xjh186164-del/Wearable-sEMG-IMU-gesture-recognition/Data/training_runs/p001_ablation_20260908/retrained/fixed_50_50/seed_20260821/test_predictions.csv

dataset_index | session_id | trial_id | true_index | true_label | fixed_50_50_index | fixed_50_50_label
10472 | S003_D08_R01 | 1 | 0 | REST | 0 | REST
10473 | S003_D08_R01 | 1 | 0 | REST | 0 | REST
10474 | S003_D08_R01 | 1 | 0 | REST | 0 | REST
10475 | S003_D08_R01 | 1 | 0 | REST | 0 | REST
10476 | S003_D08_R01 | 1 | 0 | REST | 0 | REST
10477 | S003_D08_R01 | 1 | 0 | REST | 0 | REST
10478 | S003_D08_R01 | 1 | 0 | REST | 0 | REST
10479 | S003_D08_R01 | 1 | 0 | REST | 0 | REST
10480 | S003_D08_R01 | 1 | 6 | ARM_DOWN | 6 | ARM_DOWN
10481 | S003_D08_R01 | 1 | 6 | ARM_DOWN | 6 | ARM_DOWN
10482 | S003_D08_R01 | 1 | 6 | ARM_DOWN | 6 | ARM_DOWN
10483 | S003_D08_R01 | 1 | 6 | ARM_DOWN | 6 | ARM_DOWN
10484 | S003_D08_R01 | 1 | 6 | ARM_DOWN | 6 | ARM_DOWN
10485 | S003_D08_R01 | 1 | 6 | ARM_DOWN | 6 | ARM_DOWN
10486 | S003_D08_R01 | 1 | 6 | ARM_DOWN | 6 | ARM_DOWN
10487 | S003_D08_R01 | 1 | 6 | ARM_DOWN | 6 | ARM_DOWN
10488 | S003_D08_R01 | 1 | 6 | ARM_DOWN | 6 | ARM_DOWN
10489 | S003_D08_R01 | 1 | 6 | ARM_DOWN | 6 | ARM_DOWN
10490 | S003_D08_R01 | 1 | 6 | ARM_DOWN | 6 | ARM_DOWN
10491 | S003_D08_R01 | 1 | 6 | ARM_DOWN | 6 | ARM_DOWN
10492 | S003_D08_R01 | 1 | 6 | ARM_DOWN | 6 | ARM_DOWN
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
