xjh186164-del/Wearable-sEMG-IMU-gesture-recognition/Data/validation/rld/rld_usb_quantitative_comparison.png

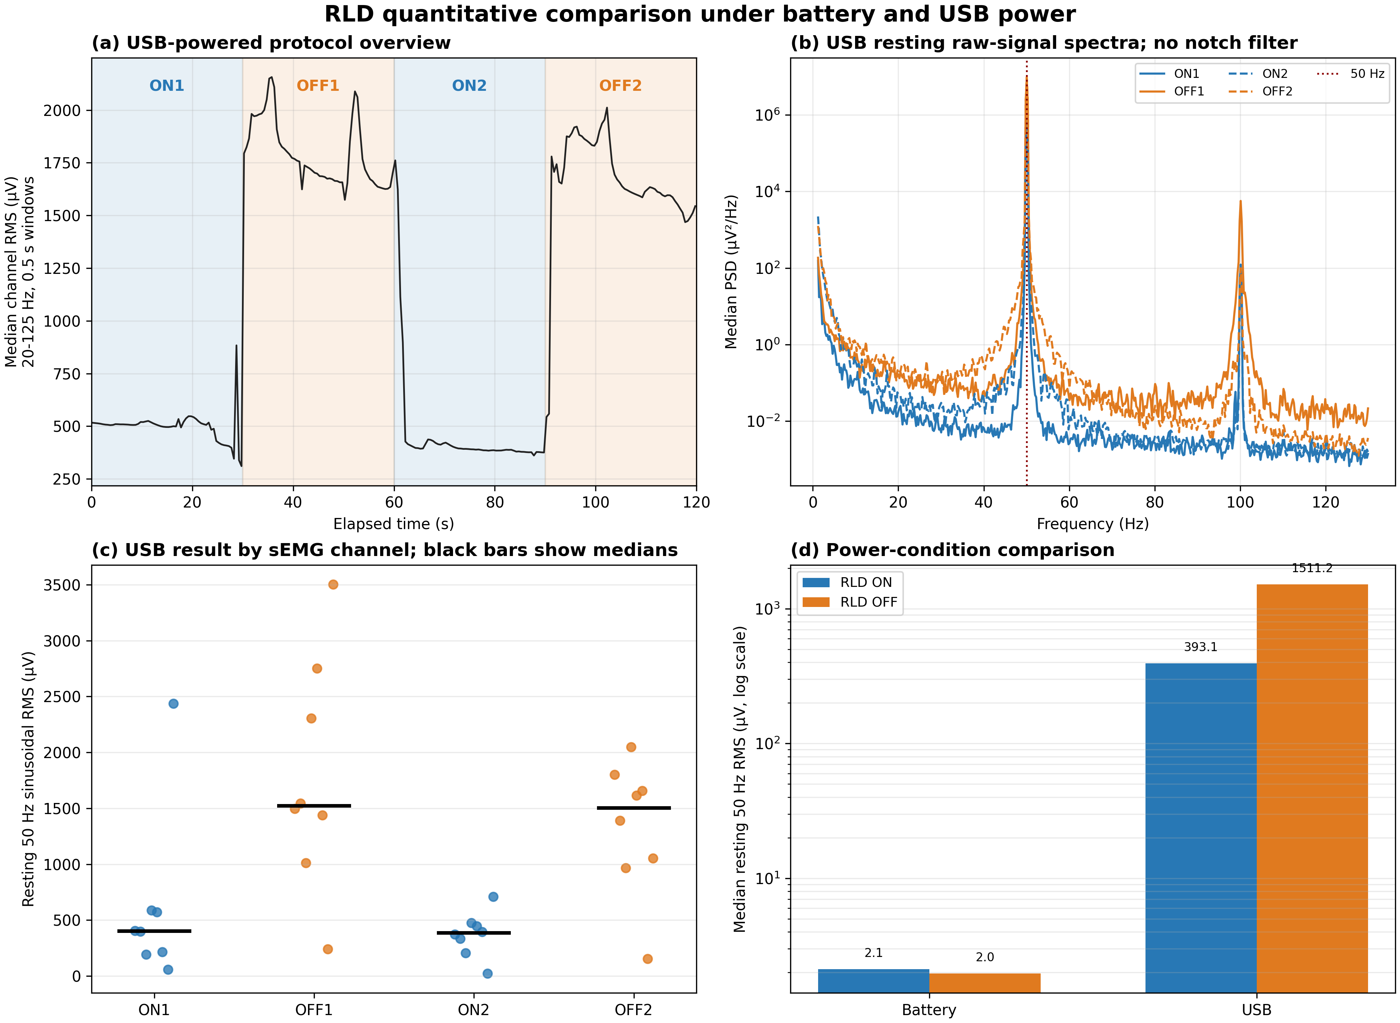
Data/validation/rld/rld_usb_quantitative_comparison.png
